emilyasterjones/chronic_NPX_mouse/2.0_probe/Flex_holder_1.stl

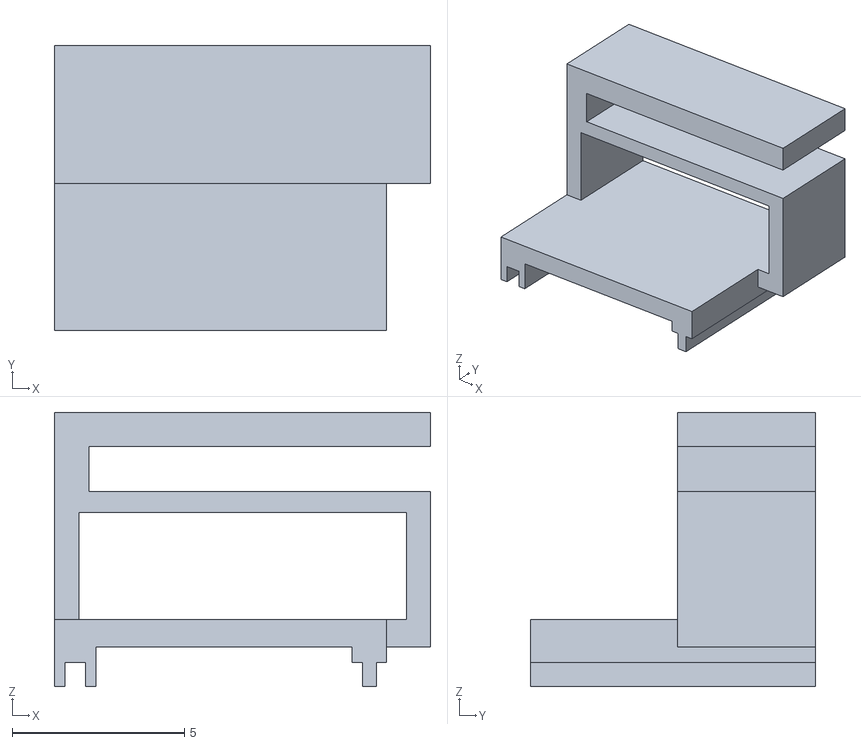
[picture p17: CAD file, 2023-12-05]
2.0_probe/Flex_holder_1.stl
10.9 x 8.26 x 7.96
