emilyasterjones/chronic_NPX_mouse/2.1_design/20_probe_clamp_hinge_pin.step

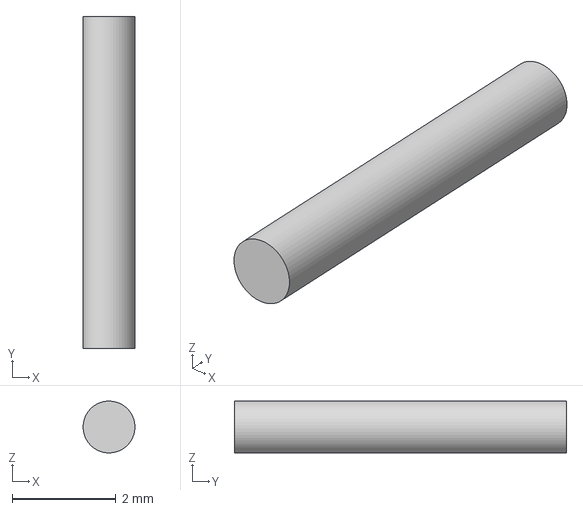
[picture p18: CAD file, 2024-02-12]
2.1_design/20_probe_clamp_hinge_pin.step
0.999 x 6.40 x 1 mm
