emilyasterjones/chronic_NPX_mouse/accessories/Battery Breakout.stl

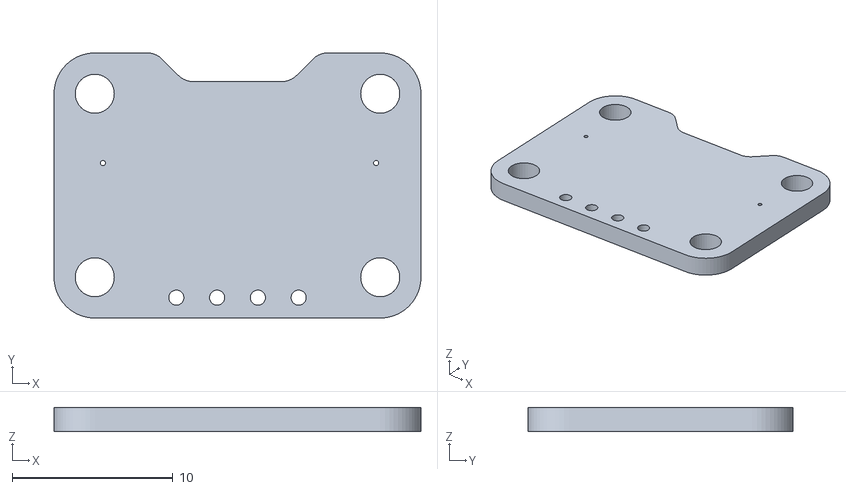
[picture p19: CAD file, 2022-10-31]
accessories/Battery Breakout.stl
22.9 x 16.5 x 1.50
