emilyasterjones/chronic_NPX_mouse/headforks/Stereotax_headbar_adapter.step

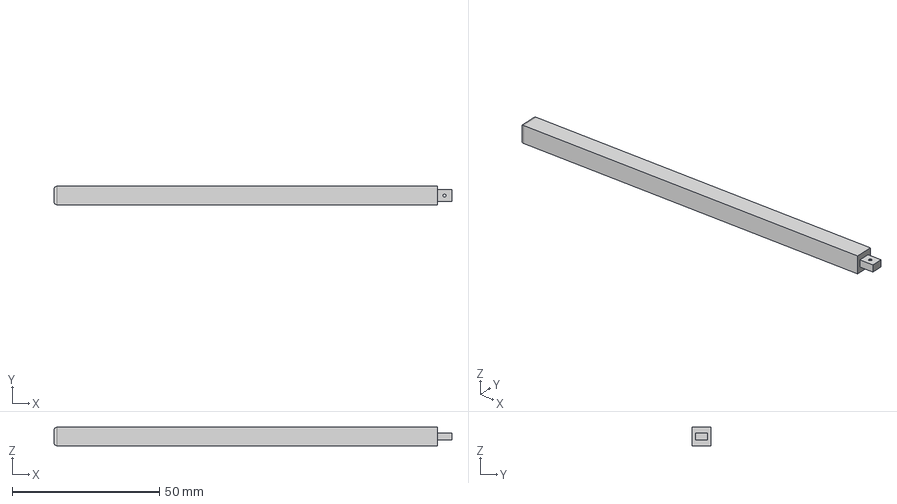
[picture p20: CAD file, 2022-10-31]
headforks/Stereotax_headbar_adapter.step
135.0 x 6.30 x 6.30 mm
