emilyasterjones/chronic_NPX_mouse/2.0_beta_probes/Dome.stl

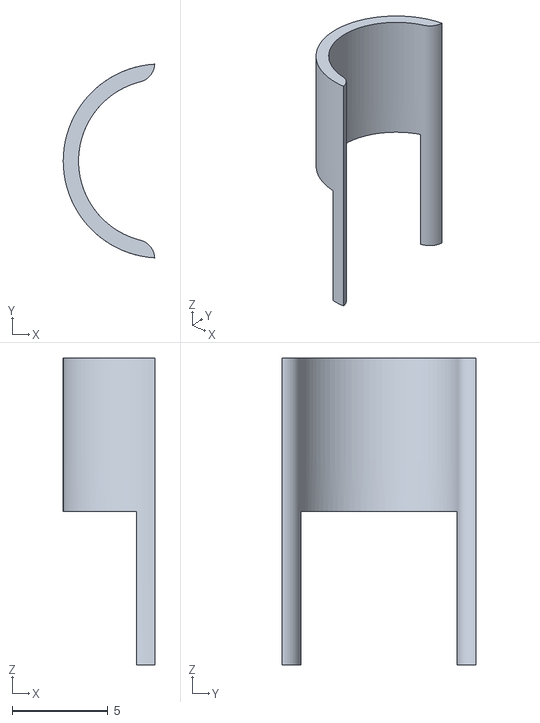
[picture p21: CAD file, 2022-12-18]
2.0_beta_probes/Dome.stl
4.77 x 10.1 x 16.0
