emilyasterjones/chronic_NPX_mouse/2.0_probe/Flex_holder_2.stl

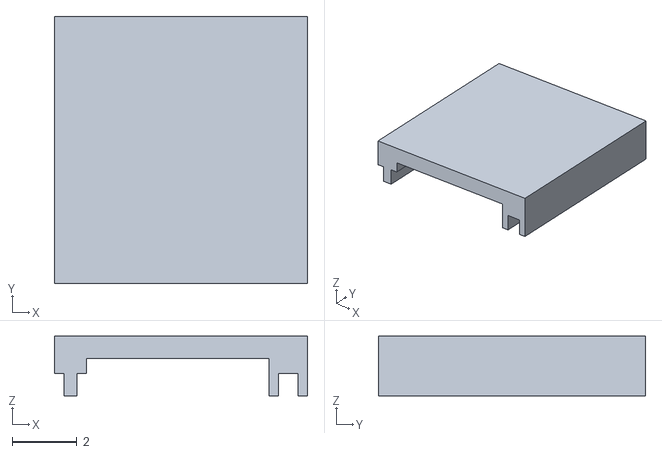
[picture p22: CAD file, 2023-12-05]
2.0_probe/Flex_holder_2.stl
7.83 x 8.26 x 1.85
