emilyasterjones/chronic_NPX_mouse/2.1_design/Flex_holder_1_with_headstage_20beta.stl

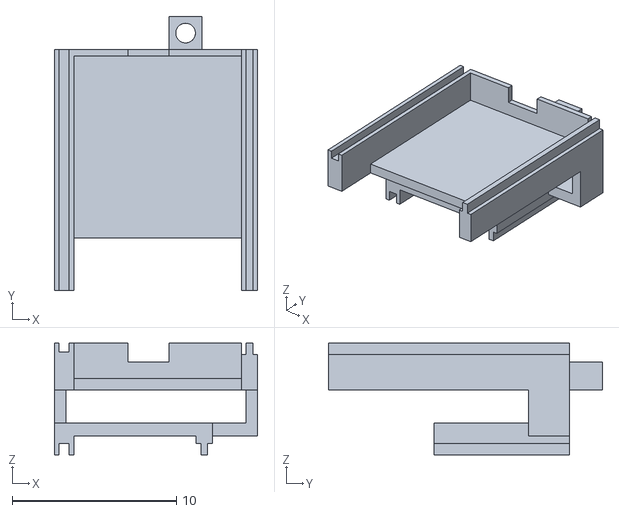
[picture p23: CAD file, 2023-12-05]
2.1_design/Flex_holder_1_with_headstage_20beta.stl
12.4 x 16.7 x 6.81
