emilyasterjones/chronic_NPX_mouse/accessories/LED_joined.stl

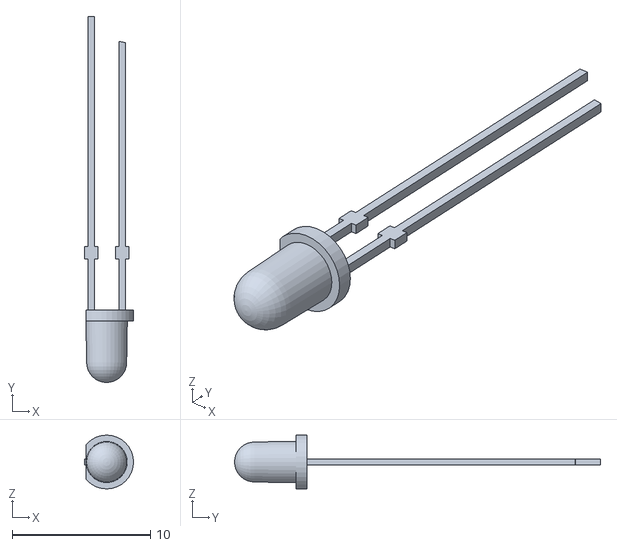
[picture p24: CAD file, 2022-10-31]
accessories/LED_joined.stl
3.56 x 26.5 x 3.90
