emilyasterjones/chronic_NPX_mouse/1.0_probe/Headstage_holder.stl

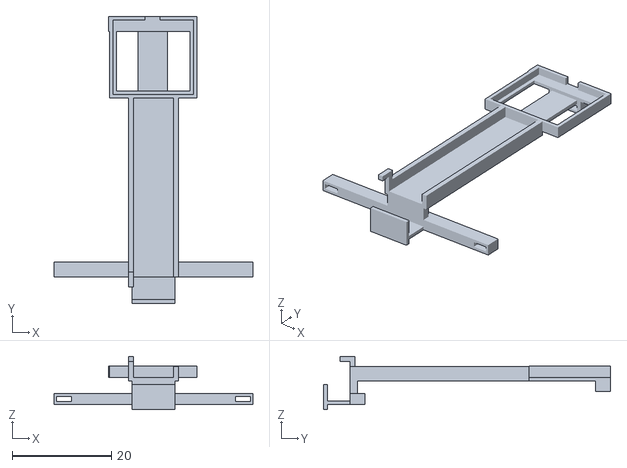
[picture p25: CAD file, 2022-10-31]
1.0_probe/Headstage_holder.stl
40.0 x 57.7 x 10.7
