emilyasterjones/chronic_NPX_mouse/2.0_beta_probes/Flex_holder_2.stl

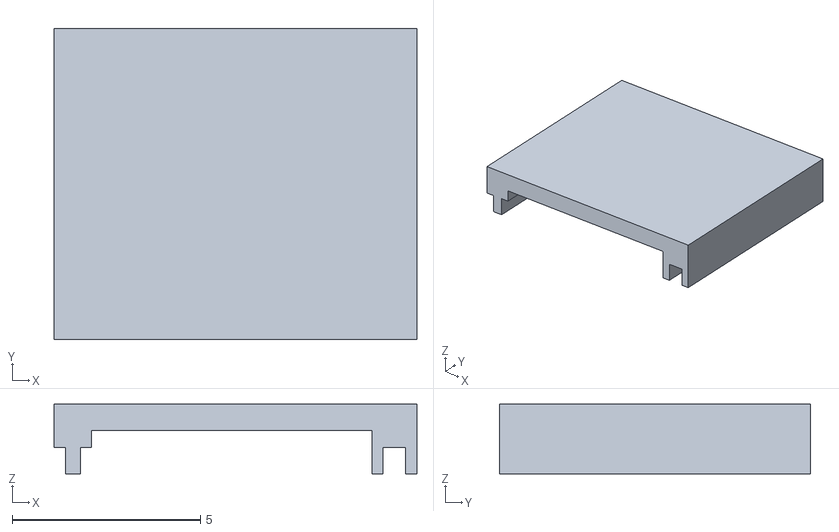
[picture p26: CAD file, 2022-12-18]
2.0_beta_probes/Flex_holder_2.stl
9.63 x 8.26 x 1.85
