emilyasterjones/chronic_NPX_mouse/2.0_probe/Probe_with_dovetail.step

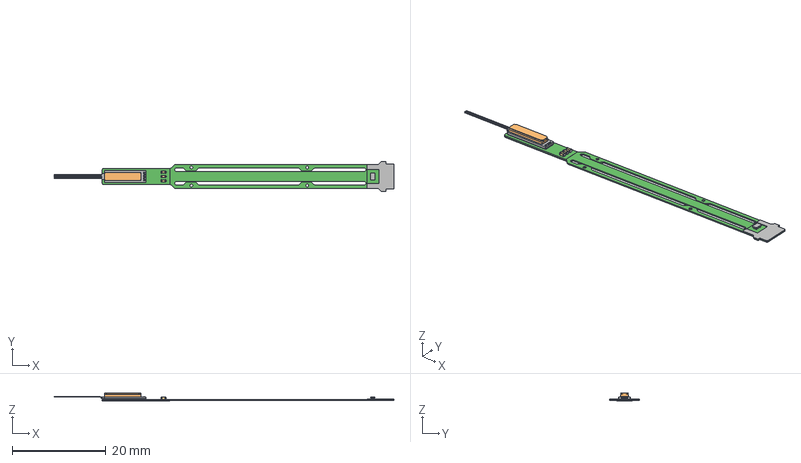
[picture p27: CAD file, 2023-12-05]
2.0_probe/Probe_with_dovetail.step
72.4 x 6.40 x 1.75 mm
VCSP50L1_ROM_edit_RGB8421504
J009777_NEUROPIXELS_DOVE_TAIL_MOUNT_GEN_2_NARROW_Rev_D
Extruded x 52
CerCap_0402 x 3
