emilyasterjones/chronic_NPX_mouse/2.1_design/Flex_holder_1_with_headstage_wide_20real.stl

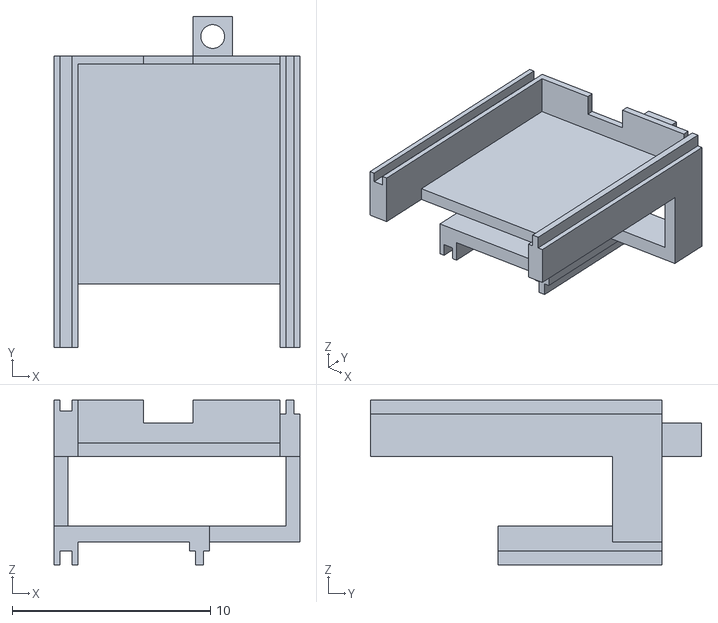
[picture p28: CAD file, 2023-12-05]
2.1_design/Flex_holder_1_with_headstage_wide_20real.stl
12.4 x 16.7 x 8.31
