emilyasterjones/chronic_NPX_mouse/1.0_probe/Dome.stl

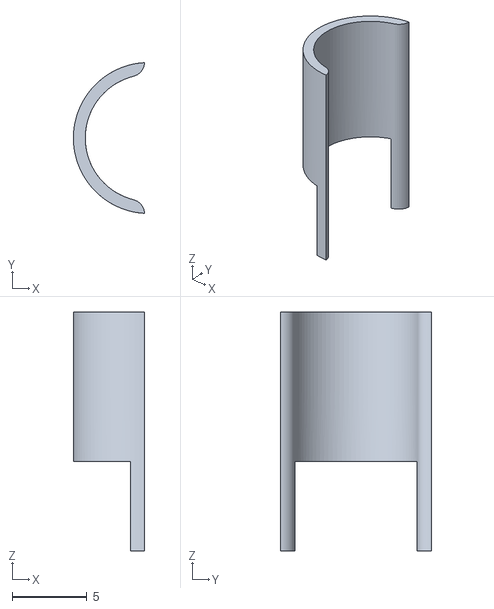
[picture p29: CAD file, 2022-10-31]
1.0_probe/Dome.stl
4.77 x 10.1 x 16.0
