emilyasterjones/chronic_NPX_mouse/2.0_probe/Flex_holder_2_with_dovetail.stl

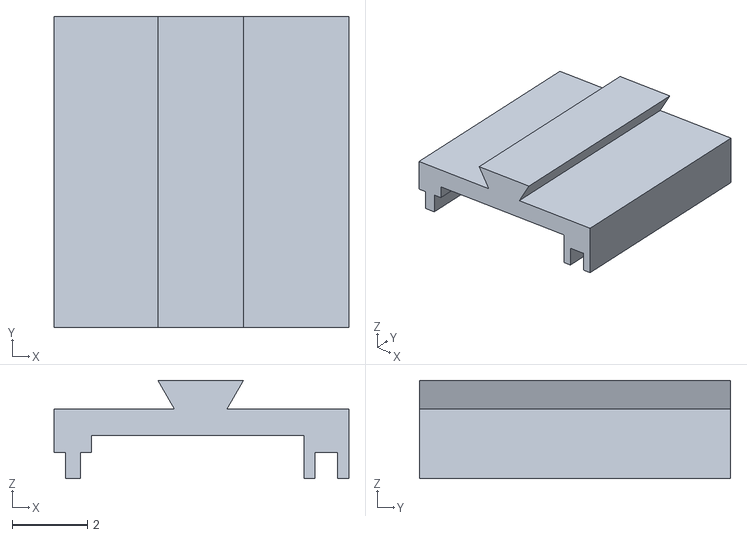
[picture p30: CAD file, 2023-12-05]
2.0_probe/Flex_holder_2_with_dovetail.stl
7.83 x 8.26 x 2.61
