emilyasterjones/chronic_NPX_mouse/2.1_design/Dome_single_probe.stl

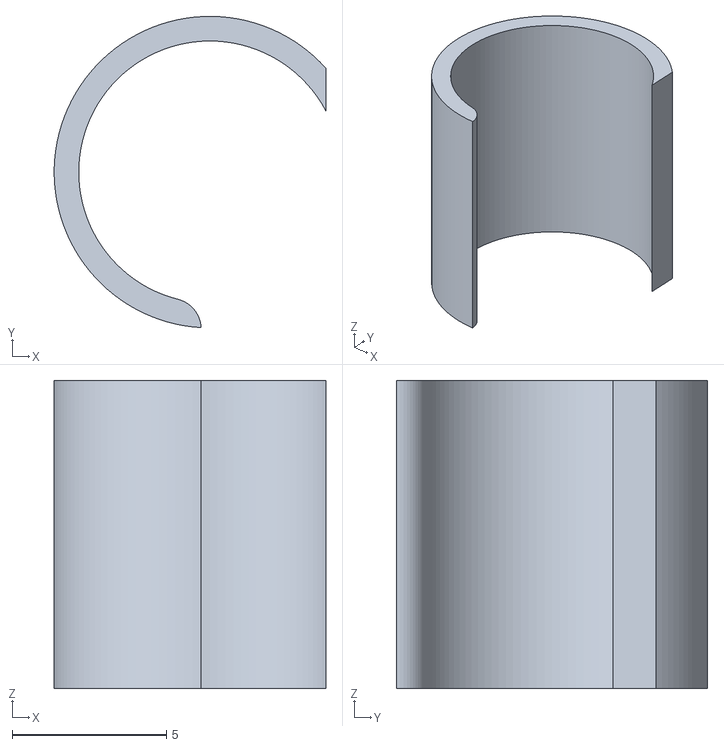
[picture p31: CAD file, 2023-12-05]
2.1_design/Dome_single_probe.stl
8.82 x 10.1 x 10.0
