emilyasterjones/chronic_NPX_mouse/1.0_probe/Flex_holder_2.stl

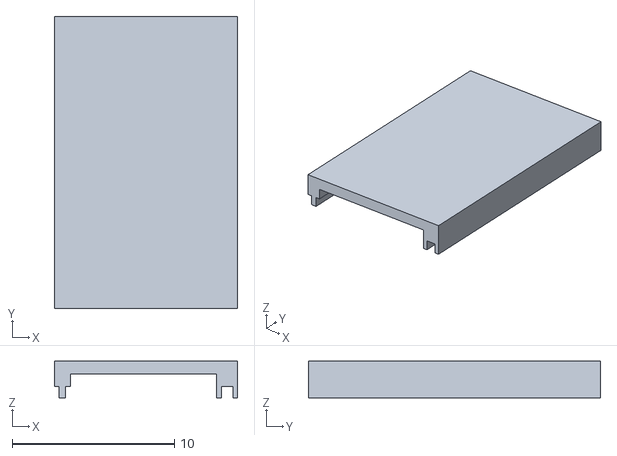
[picture p32: CAD file, 2022-10-31]
1.0_probe/Flex_holder_2.stl
11.3 x 18.0 x 2.25
