emilyasterjones/chronic_NPX_mouse/2.0_beta_probes/Flex_holder_2_with_dovetail.stl

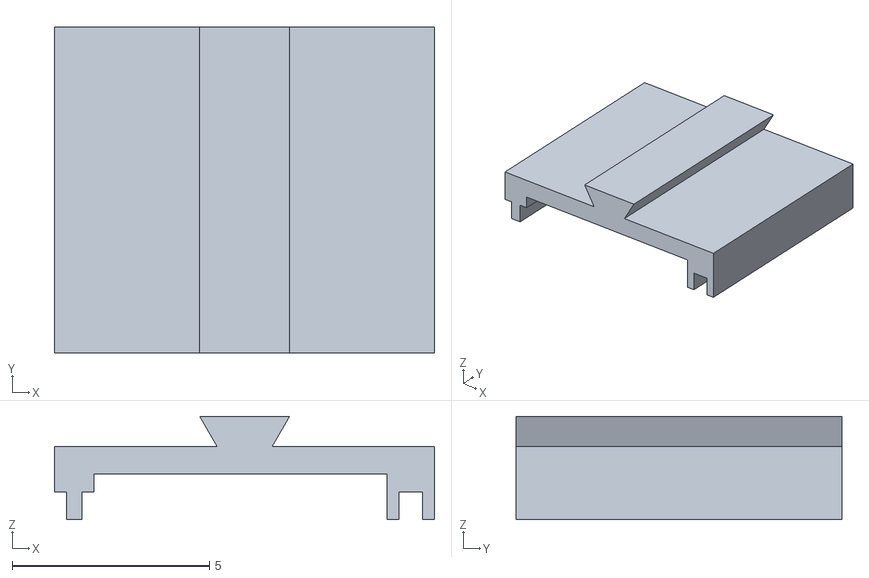
[picture p33: CAD file, 2022-12-18]
2.0_beta_probes/Flex_holder_2_with_dovetail.stl
9.63 x 8.26 x 2.61
