emilyasterjones/chronic_NPX_mouse/2.0_beta_probes/Body_piece_right.stl

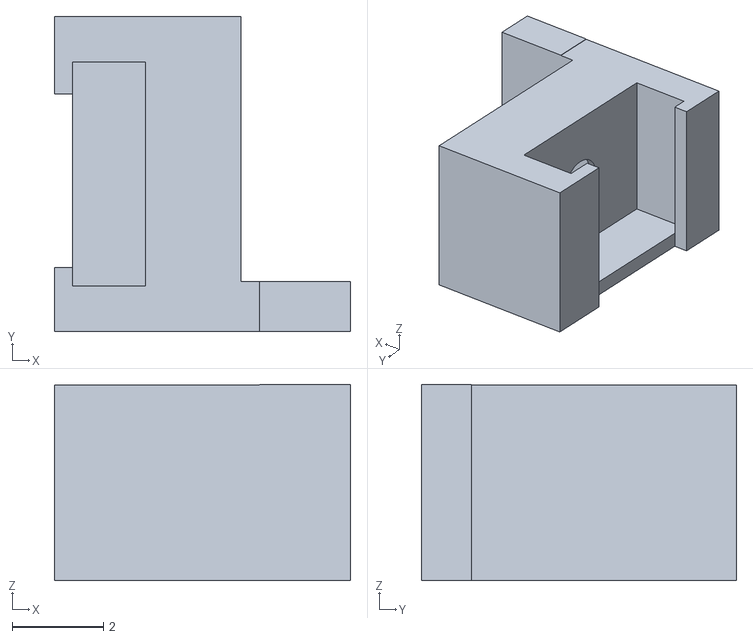
[picture p35: CAD file, 2022-12-08]
2.0_beta_probes/Body_piece_right.stl
6.49 x 6.90 x 4.30
