emilyasterjones/chronic_NPX_mouse/2.1_design/Body_piece_right_30deg.stl

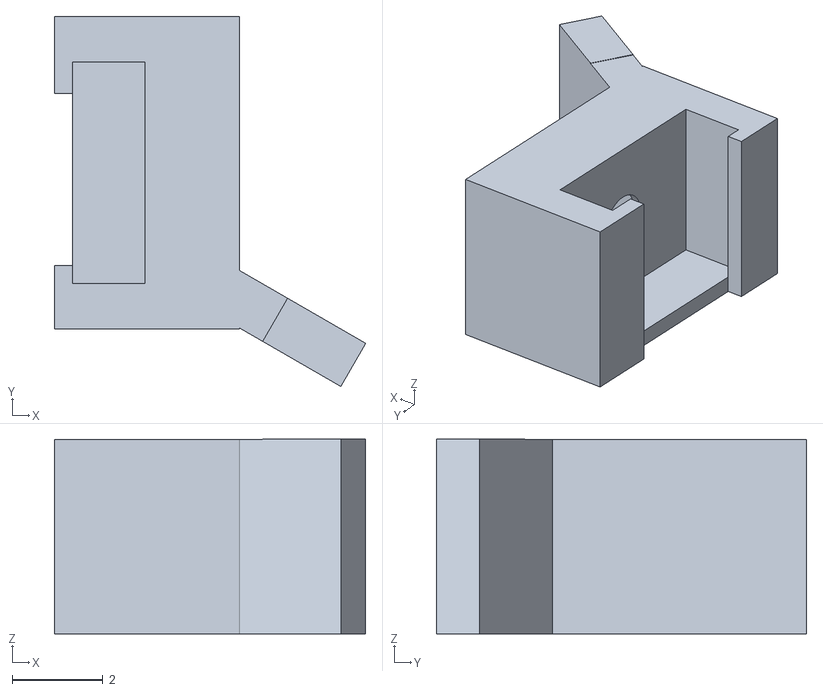
[picture p36: CAD file, 2023-12-05]
2.1_design/Body_piece_right_30deg.stl
6.88 x 8.17 x 4.30
