emilyasterjones/chronic_NPX_mouse/2.1_design/Headstage_dust_cover.stl

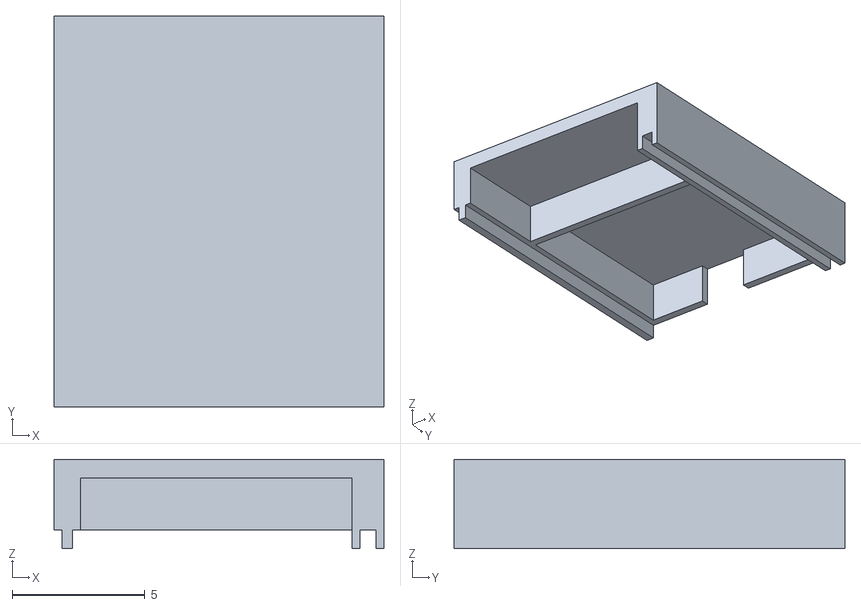
[picture p37: CAD file, 2023-12-05]
2.1_design/Headstage_dust_cover.stl
12.4 x 14.7 x 3.35
