emilyasterjones/chronic_NPX_mouse/2.0_beta_probes/Dovetail.stl

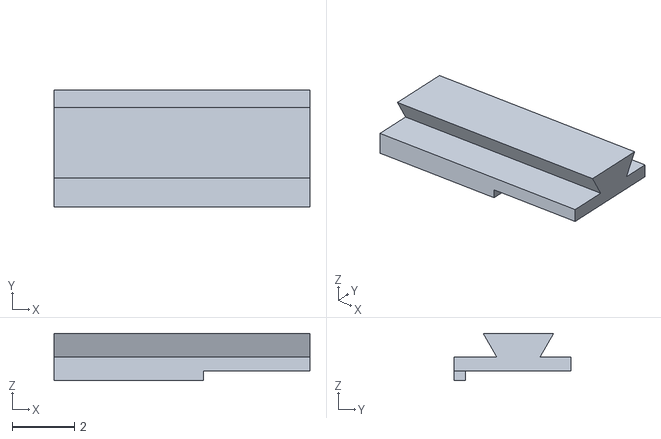
[picture p38: CAD file, 2022-12-08]
2.0_beta_probes/Dovetail.stl
8.26 x 3.78 x 1.52
