emilyasterjones/chronic_NPX_mouse/2.1_design/Body_piece_left.stl

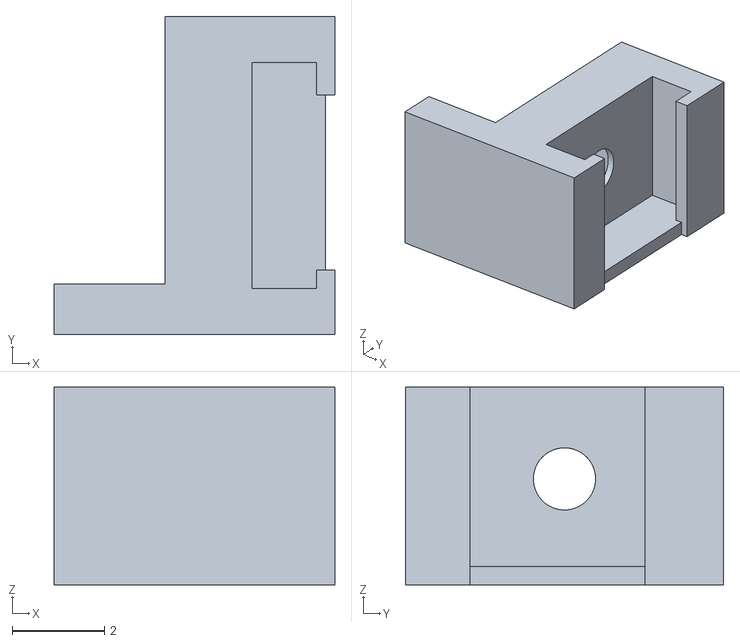
[picture p40: CAD file, 2023-11-23]
2.1_design/Body_piece_left.stl
6.09 x 6.90 x 4.29
