emilyasterjones/chronic_NPX_mouse/2.1_design/Wings.stl

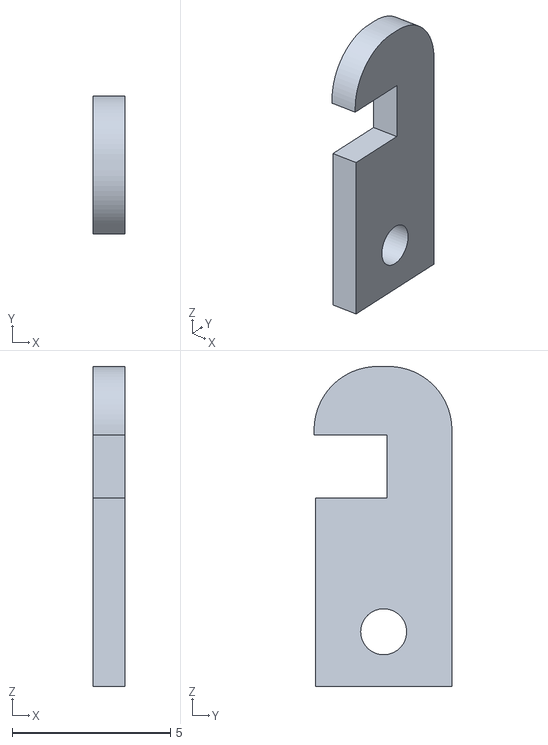
[picture p41: CAD file, 2023-11-23]
2.1_design/Wings.stl
1.00 x 4.35 x 10.1
